addmix/stm32-hid-device/CAD files/stl/NutHolder.stl

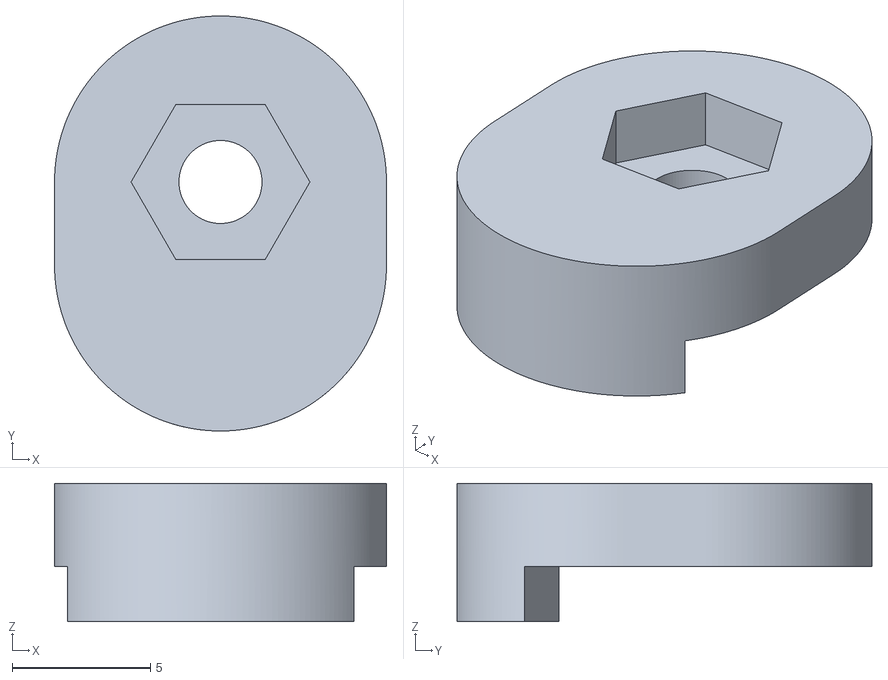
[picture p16: CAD file, 2026-04-22]
CAD files/stl/NutHolder.stl
12.0 x 15.0 x 5.00
