addmix/stm32-hid-device/CAD files/stl/MountRail.stl

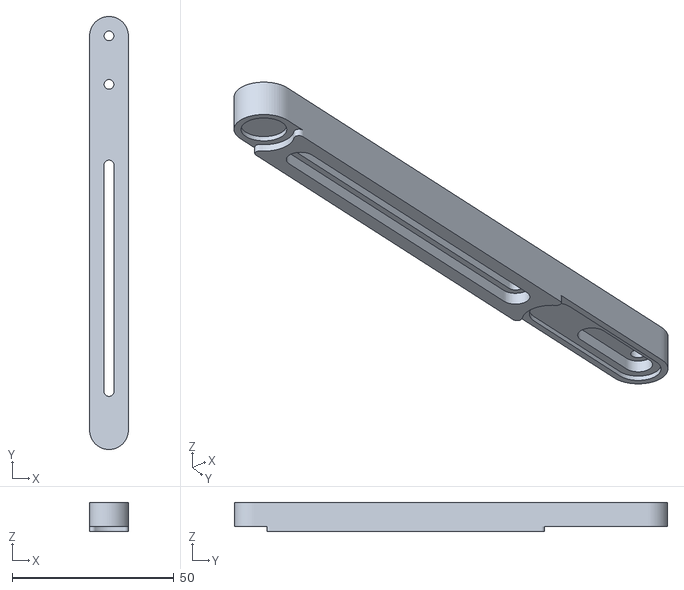
[picture p17: CAD file, 2026-04-22]
CAD files/stl/MountRail.stl
12.0 x 134.0 x 9.00
